francis-walsh/phoenix-down/Firmware/Core/Inc/PID.h

/*
 * PID.h
 *
 *  Created on: Feb 20, 2022
 *      Author: Frank Walsh
 */

#ifndef INC_PID_H_
#define INC_PID_H_

typedef struct {

	/* Controller gains */
	float Kp;
	float Ki;
	float Kd;

	/* Derivative low-pass filter time constant */
	float tau;

	/* Output limits */
	float limMin;
	float limMax;

	/* Integrator limits */
	float limMinInt;
	float limMaxInt;

	/* Sample time (in seconds) */
	float T;

	/* Controller "memory" */
	float integrator;
	float prevError;			/* Required for integrator */
	float differentiator;
	float prevMeasurement;		/* Required for differentiator */

	/* Controller output */
	float out;

} PIDController;

void  PIDController_Init(PIDController *pid);
float PIDController_Update(PIDController *pid, float setpoint, float measurement);

#endif /* INC_PID_H_ */
