francis-walsh/phoenix-down/Firmware/arduinoCAN/woodStoveCAN/woodStoveCAN.ino

/****************************************************************************
CAN Read Demo for the SparkFun CAN Bus Shield. 

Written by Stephen McCoy. 
Original tutorial available here: http://www.instructables.com/id/CAN-Bus-Sniffing-and-Broadcasting-with-Arduino
Used with permission 2016. License CC By SA. 

Distributed as-is; no warranty is given.
*************************************************************************/

#include <Canbus.h>
#include <defaults.h>
#include <global.h>
#include <mcp2515.h>
#include <mcp2515_defs.h>

//********************************Setup Loop*********************************//

// Added vars
int bytes = 0;

void setup() {
  Serial.begin(9600); // For debug use
  Serial.println("CAN Read - Testing receival of CAN Bus message");  
  delay(1000);
  
  if(Canbus.init(CANSPEED_250))  //Initialise MCP2515 CAN controller at the specified speed
    Serial.println("CAN Init ok");
  else
    Serial.println("Can't init CAN");
    
  delay(1000);
}

//********************************Main Loop*********************************//

void loop()
{
  tCAN message;
  
  if (mcp2515_check_message()) 
  {
    if (mcp2515_get_message(&message)) 
	  {    
     Serial.print("ID: ");
     Serial.print(message.id,HEX);
     Serial.print(", ");
     Serial.print("Data: ");
     for(int i=0;i<message.header.length;i++) 
      {	
        Serial.print(message.data[i],HEX);
        Serial.print(" ");
      }
     Serial.println("");
    }
  
  
    }

    // Serial write commands
  // Pong test
    bytes = Serial.read();
    
    if(bytes == 0xFF)
    {
      Serial.println("pong");
    }
  
  
    if(bytes >= 0x00)
    {
      Serial.println(bytes);
    // CAN Write function
    // Bytes is the data from the python script
    // Need to send the data stored in 'bytes' through CAN interface
      // Send CAN message
      message.id = 0x631; //formatted in HEX
      message.header.rtr = 0;
      message.header.length = 1; //formatted in DEC
      message.data[0] = bytes;
    
      mcp2515_bit_modify(CANCTRL, (1<<REQOP2)|(1<<REQOP1)|(1<<REQOP0), 0);
      mcp2515_send_message(&message);
  
      delay(500);
      
    }


}
